ragul-sj-005/FIFO-Management-for-Comestible-Storage-Units/Thermal_Printer.SLDPRT

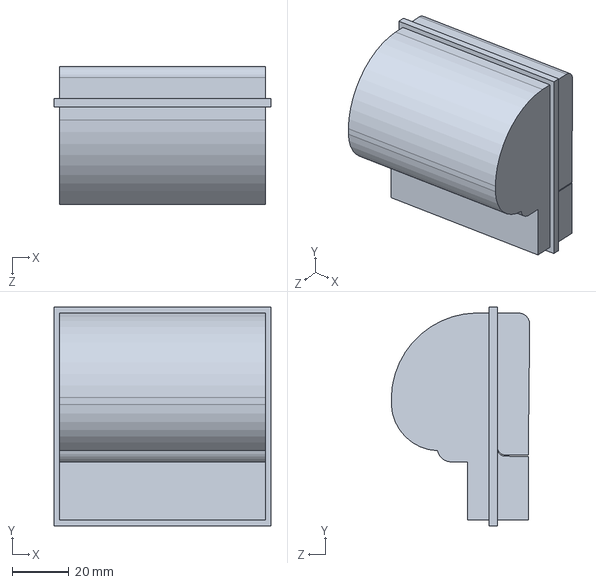
[picture p15: CAD file, 2026-06-11]
Thermal_Printer.SLDPRT
76.8 x 77.4 x 49.0 mm
